gzowski/Somei70/PCB/somei70.kicad_sch

## KiCad design PCB/somei70.kicad_sch (2024-09-26)

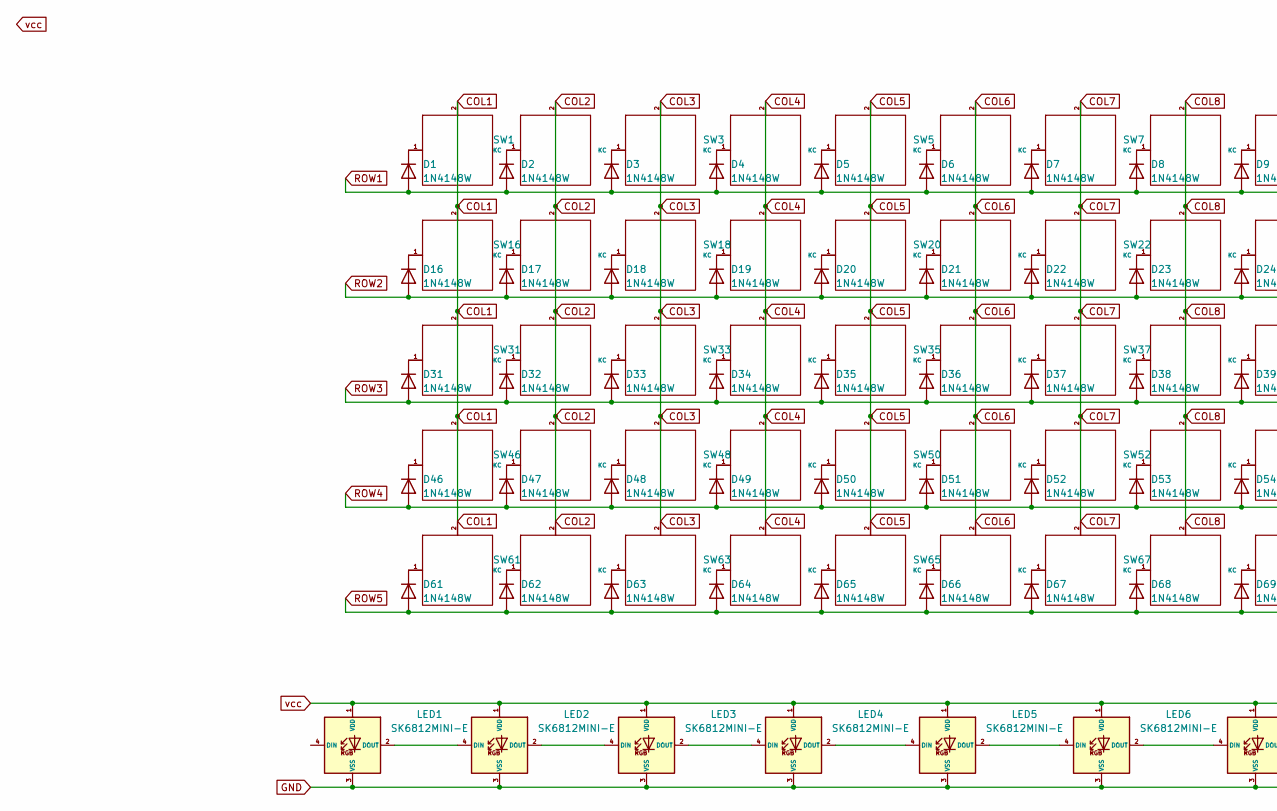
[picture p8: schematic somei70.kicad_sch, part in row 1, column 1]

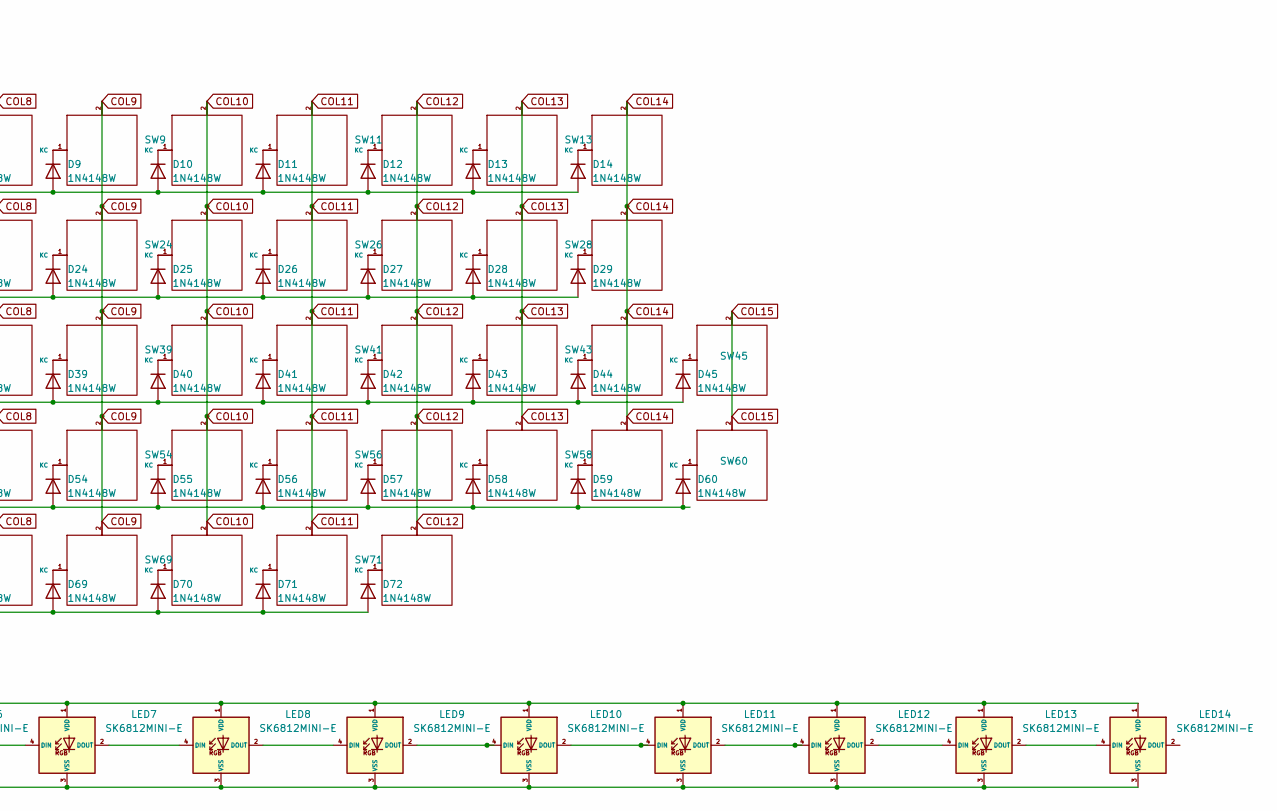
[picture p9: schematic somei70.kicad_sch, part in row 1, column 2]

Parts:
D1, D2, D3, D4, D5, D6, D7, D8, D9, D10, D11, D12, D13, D14, D16, D17, D18, D19, D20, D21, D22, D23, D24, D25, D26, D27, D28, D29, D31, D32, D33, D34, D35, D36, D37, D38, D39, D40, D41, D42, D43, D44, D45, D46, D47, D48, D49, D50, D51, D52, D53, D54, D55, D56, D57, D58, D59, D60, D61, D62, D63, D64, D65, D66, D67, D68, D69, D70, D71, D72: 1N4148W; D_SOD-123F
LED1, LED2, LED3, LED4, LED5, LED6, LED7, LED8, LED9, LED10, LED11, LED12, LED13, LED14: SK6812MINI-E; SK6812MINI_3535_6028_3.2x2.8mm_Round
SW1, SW2, SW3, SW4, SW5, SW6, SW7, SW8, SW9, SW10, SW11, SW12, SW13, SW14, SW16, SW17, SW18, SW19, SW20, SW21, SW22, SW23, SW24, SW25, SW26, SW27, SW28, SW29, SW31, SW32, SW33, SW34, SW35, SW36, SW37, SW38, SW39, SW40, SW41, SW42, SW43, SW44, SW45, SW46, SW47, SW48, SW49, SW50, SW51, SW52, SW53, SW54, SW55, SW56, SW57, SW58, SW59, SW60, SW61, SW62, SW63, SW64, SW65, SW66, SW67, SW68, SW69, SW70, SW71, SW72: CPG151101S11; SW_Cherry_MX_1.00u_PCB_HOTSWAP_Details

Connections:
COL1: SW1.2, SW16.2, SW31.2, SW46.2, SW61.2
COL2: SW2.2, SW17.2, SW32.2, SW47.2, SW62.2
COL3: SW3.2, SW18.2, SW33.2, SW48.2, SW63.2
COL4: SW4.2, SW19.2, SW34.2, SW49.2, SW64.2
COL5: SW5.2, SW20.2, SW35.2, SW50.2, SW65.2
COL6: SW6.2, SW21.2, SW36.2, SW51.2, SW66.2
COL7: SW7.2, SW22.2, SW37.2, SW52.2, SW67.2
COL8: SW8.2, SW23.2, SW38.2, SW53.2, SW68.2
COL9: SW9.2, SW24.2, SW39.2, SW54.2, SW69.2
COL10: SW10.2, SW25.2, SW40.2, SW55.2, SW70.2
COL11: SW11.2, SW26.2, SW41.2, SW56.2, SW71.2
COL12: SW12.2, SW27.2, SW42.2, SW57.2, SW72.2
COL13: SW13.2, SW28.2, SW43.2, SW58.2
COL14: SW14.2, SW29.2, SW44.2, SW59.2
COL15: SW45.2, SW60.2
GND: LED1.3 (VSS), LED2.3 (VSS), LED3.3 (VSS), LED4.3 (VSS), LED5.3 (VSS), LED6.3 (VSS), LED7.3 (VSS), LED8.3 (VSS), LED9.3 (VSS), LED10.3 (VSS), LED11.3 (VSS), LED12.3 (VSS), LED13.3 (VSS), LED14.3 (VSS)
unnamed: D1.1 (K), SW1.1
unnamed: D2.1 (K), SW2.1
unnamed: D3.1 (K), SW3.1
unnamed: D4.1 (K), SW4.1
unnamed: D5.1 (K), SW5.1
unnamed: D6.1 (K), SW6.1
unnamed: D7.1 (K), SW7.1
unnamed: D8.1 (K), SW8.1
unnamed: D9.1 (K), SW9.1
unnamed: D10.1 (K), SW10.1
unnamed: D11.1 (K), SW11.1
unnamed: D12.1 (K), SW12.1
unnamed: D13.1 (K), SW13.1
unnamed: D14.1 (K), SW14.1
unnamed: D16.1 (K), SW16.1
unnamed: D17.1 (K), SW17.1
unnamed: D18.1 (K), SW18.1
unnamed: D19.1 (K), SW19.1
unnamed: D20.1 (K), SW20.1
unnamed: D21.1 (K), SW21.1
unnamed: D22.1 (K), SW22.1
unnamed: D23.1 (K), SW23.1
unnamed: D24.1 (K), SW24.1
unnamed: D25.1 (K), SW25.1
unnamed: D26.1 (K), SW26.1
unnamed: D27.1 (K), SW27.1
unnamed: D28.1 (K), SW28.1
unnamed: D29.1 (K), SW29.1
unnamed: D31.1 (K), SW31.1
unnamed: D32.1 (K), SW32.1
unnamed: D33.1 (K), SW33.1
unnamed: D34.1 (K), SW34.1
unnamed: D35.1 (K), SW35.1
unnamed: D36.1 (K), SW36.1
unnamed: D37.1 (K), SW37.1
unnamed: D38.1 (K), SW38.1
unnamed: D39.1 (K), SW39.1
unnamed: D40.1 (K), SW40.1
unnamed: D41.1 (K), SW41.1
unnamed: D42.1 (K), SW42.1
unnamed: D43.1 (K), SW43.1
unnamed: D44.1 (K), SW44.1
unnamed: D45.1 (K), SW45.1
unnamed: D46.1 (K), SW46.1
unnamed: D47.1 (K), SW47.1
unnamed: D48.1 (K), SW48.1
unnamed: D49.1 (K), SW49.1
unnamed: D50.1 (K), SW50.1
unnamed: D51.1 (K), SW51.1
unnamed: D52.1 (K), SW52.1
unnamed: D53.1 (K), SW53.1
unnamed: D54.1 (K), SW54.1
unnamed: D55.1 (K), SW55.1
unnamed: D56.1 (K), SW56.1
unnamed: D57.1 (K), SW57.1
unnamed: D58.1 (K), SW58.1
unnamed: D59.1 (K), SW59.1
unnamed: D60.1 (K), SW60.1
unnamed: D61.1 (K), SW61.1
unnamed: D62.1 (K), SW62.1
unnamed: D63.1 (K), SW63.1
unnamed: D64.1 (K), SW64.1
unnamed: D65.1 (K), SW65.1
unnamed: D66.1 (K), SW66.1
unnamed: D67.1 (K), SW67.1
unnamed: D68.1 (K), SW68.1
unnamed: D69.1 (K), SW69.1
unnamed: D70.1 (K), SW70.1
unnamed: D71.1 (K), SW71.1
unnamed: D72.1 (K), SW72.1
unnamed: LED1.2 (DOUT), LED2.4 (DIN)
unnamed: LED2.2 (DOUT), LED3.4 (DIN)
unnamed: LED3.2 (DOUT), LED4.4 (DIN)
unnamed: LED4.2 (DOUT), LED5.4 (DIN)
unnamed: LED5.2 (DOUT), LED6.4 (DIN)
unnamed: LED6.2 (DOUT), LED7.4 (DIN)
unnamed: LED7.2 (DOUT), LED8.4 (DIN)
unnamed: LED8.2 (DOUT), LED9.4 (DIN)
unnamed: LED10.2 (DOUT), LED11.4 (DIN)
unnamed: LED9.2 (DOUT), LED10.4 (DIN)
unnamed: LED11.2 (DOUT), LED12.4 (DIN)
unnamed: LED12.2 (DOUT), LED13.4 (DIN)
unnamed: LED13.2 (DOUT), LED14.4 (DIN)
ROW1: D1.2 (A), D2.2 (A), D3.2 (A), D4.2 (A), D5.2 (A), D6.2 (A), D7.2 (A), D8.2 (A), D9.2 (A), D10.2 (A), D11.2 (A), D12.2 (A), D13.2 (A), D14.2 (A)
ROW2: D16.2 (A), D17.2 (A), D18.2 (A), D19.2 (A), D20.2 (A), D21.2 (A), D22.2 (A), D23.2 (A), D24.2 (A), D25.2 (A), D26.2 (A), D27.2 (A), D28.2 (A), D29.2 (A)
ROW3: D31.2 (A), D32.2 (A), D33.2 (A), D34.2 (A), D35.2 (A), D36.2 (A), D37.2 (A), D38.2 (A), D39.2 (A), D40.2 (A), D41.2 (A), D42.2 (A), D43.2 (A), D44.2 (A), D45.2 (A)
ROW4: D46.2 (A), D47.2 (A), D48.2 (A), D49.2 (A), D50.2 (A), D51.2 (A), D52.2 (A), D53.2 (A), D54.2 (A), D55.2 (A), D56.2 (A), D57.2 (A), D58.2 (A), D59.2 (A), D60.2 (A)
ROW5: D61.2 (A), D62.2 (A), D63.2 (A), D64.2 (A), D65.2 (A), D66.2 (A), D67.2 (A), D68.2 (A), D69.2 (A), D70.2 (A), D71.2 (A), D72.2 (A)
vcc: LED1.1 (VDD), LED2.1 (VDD), LED3.1 (VDD), LED4.1 (VDD), LED5.1 (VDD), LED6.1 (VDD), LED7.1 (VDD), LED8.1 (VDD), LED9.1 (VDD), LED10.1 (VDD), LED11.1 (VDD), LED12.1 (VDD), LED13.1 (VDD), LED14.1 (VDD)
